WilliamKWusik/Wusik-44UM/Documents/DIY/Arduino Pro Micro.jpg

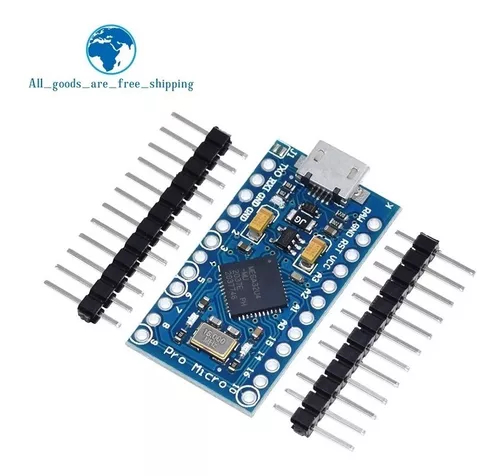
Documents/DIY/Arduino Pro Micro.jpg
