WilliamKWusik/Wusik-44UM/Documents/DIY/Button Switches.jpg

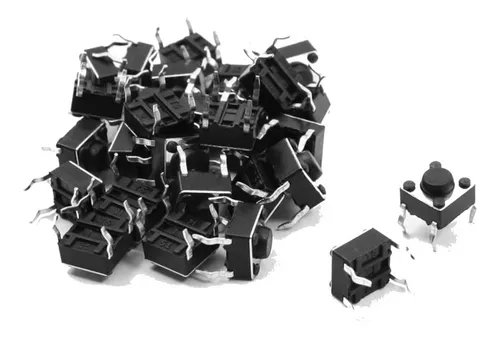
Documents/DIY/Button Switches.jpg
