WilliamKWusik/Wusik-44UM/Documents/DIY/LED Strip.jpg

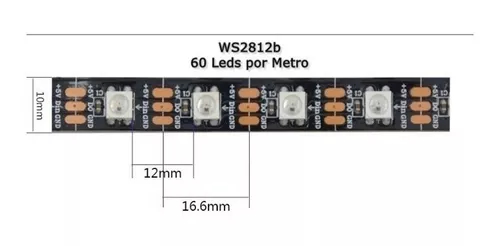
Documents/DIY/LED Strip.jpg
