WilliamKWusik/Wusik-44UM/Documents/DIY/Wires.jpg

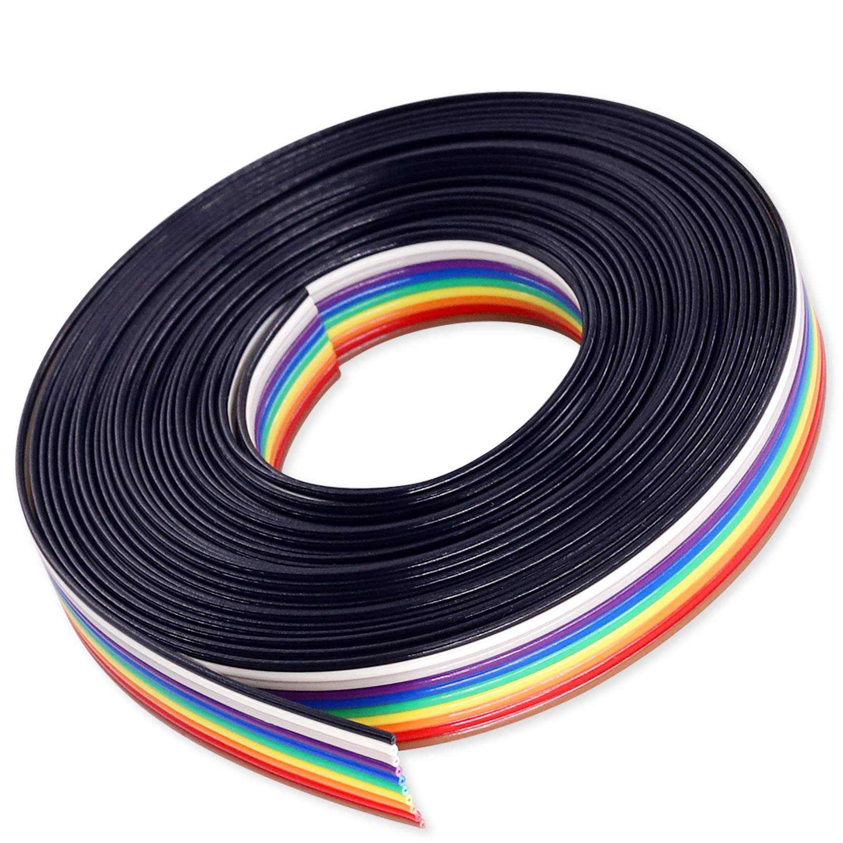
Documents/DIY/Wires.jpg
