WilliamKWusik/Wusik-44UM/Images/Picture (2).jpeg

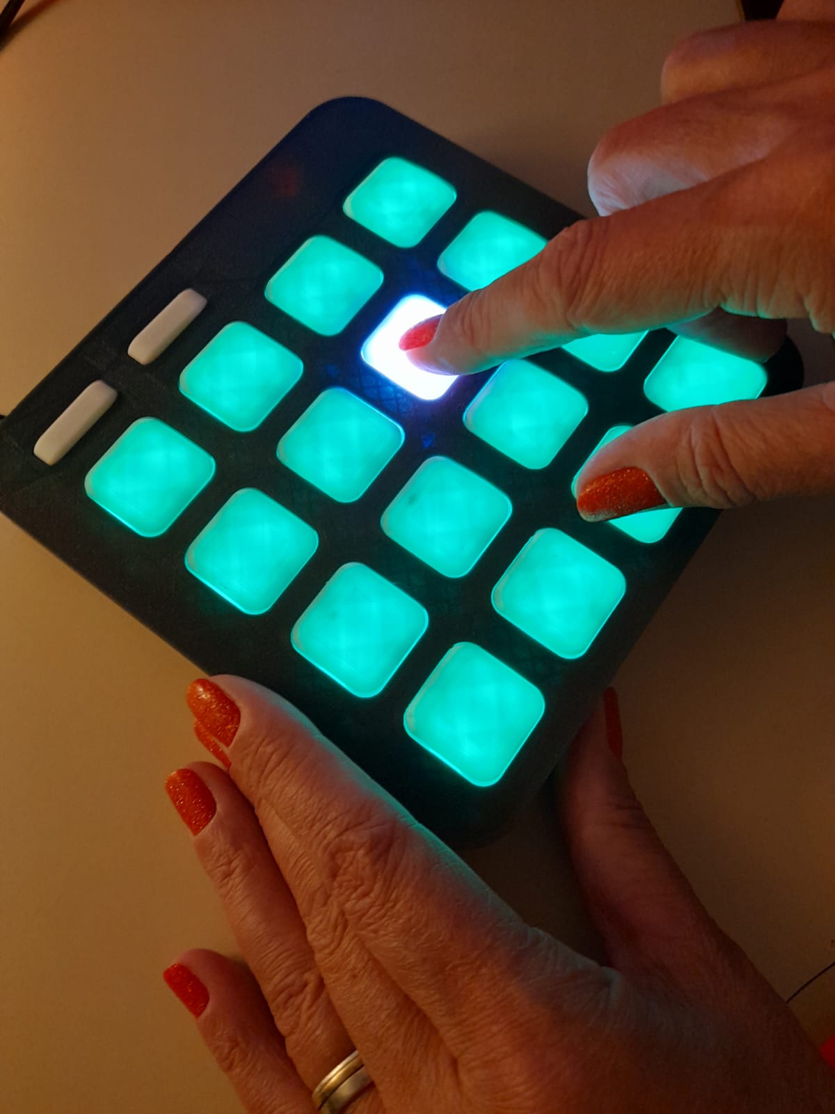
Images/Picture (2).jpeg
