WilliamKWusik/Wusik-44UM/Images/Picture (3).jpeg

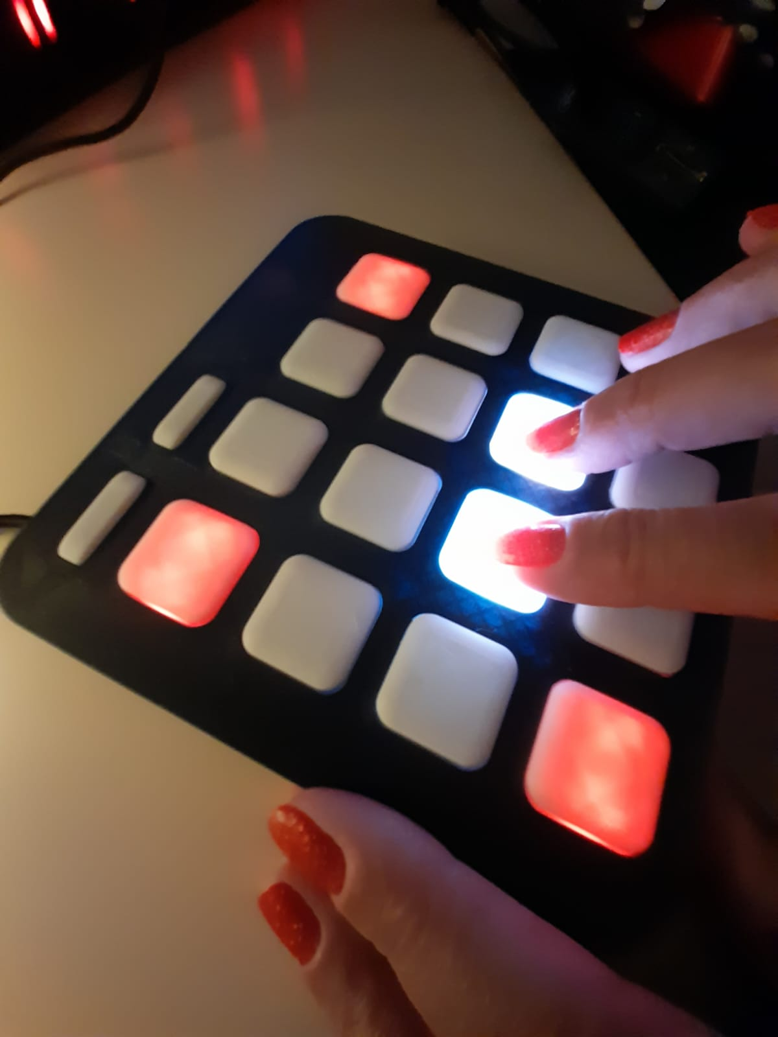
Images/Picture (3).jpeg
