WilliamKWusik/Wusik-44UM/Wusik_PR44_Performance_App/_Release/Wusik PR44 Data/Samples/PerimeterSound.com/Bio-MechanicBeats1_FreeSamplePack/_BioMechanicBeats_480.jpg

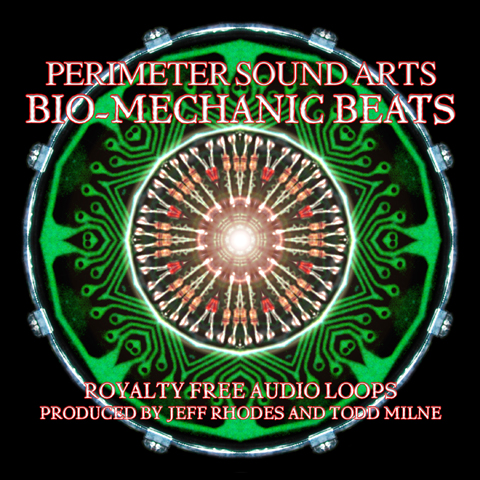
Wusik_PR44_Performance_App/_Release/Wusik PR44 Data/Samples/PerimeterSound.com/Bio-MechanicBeats1_FreeSamplePack/_BioMechanicBeats_480.jpg
