WilliamKWusik/Wusik-44UM/Wusik_PR44_Performance_App/_Release/Wusik PR44 Data/Samples/PerimeterSound.com/Bio-MechanicBeats2_FreeSamplePack/_Bio-MechanicBeats2_480.jpg

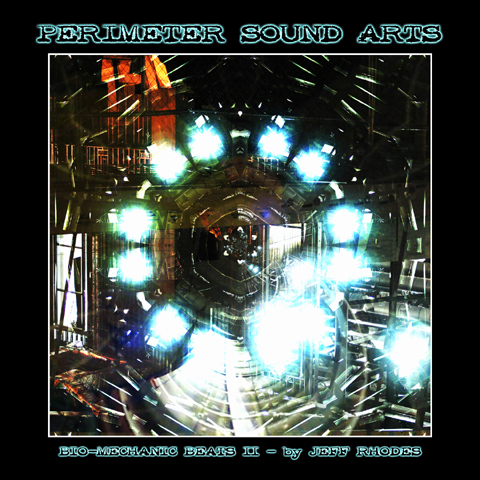
Wusik_PR44_Performance_App/_Release/Wusik PR44 Data/Samples/PerimeterSound.com/Bio-MechanicBeats2_FreeSamplePack/_Bio-MechanicBeats2_480.jpg
