WilliamKWusik/Wusik-44UM/Wusik_PR44_Performance_App/_Release/Wusik PR44 Data/Samples/PerimeterSound.com/Bio-MechanicBeats3_FreeSamplePack/Bio-MechanicBeatsIII_coverart_500X.jpg

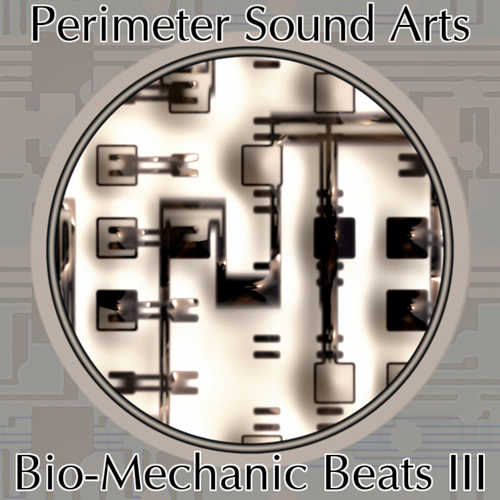
Wusik_PR44_Performance_App/_Release/Wusik PR44 Data/Samples/PerimeterSound.com/Bio-MechanicBeats3_FreeSamplePack/Bio-MechanicBeatsIII_coverart_500X.jpg
