WilliamKWusik/Wusik-44UM/Wusik_PR44_Performance_App/_Release/Wusik PR44 Data/Samples/PerimeterSound.com/AbstractWorld Fusion1_FreeSamplePack/_AbstractWorldFusion_480.jpg

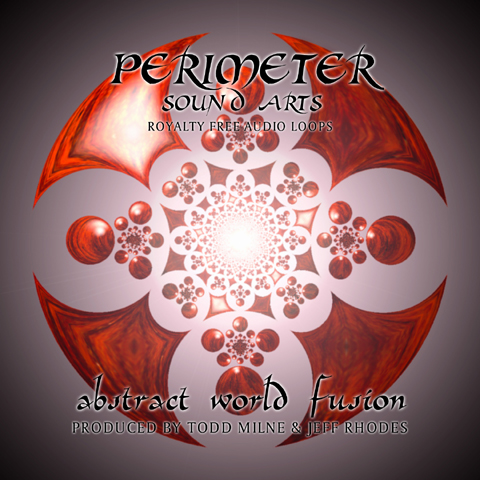
Wusik_PR44_Performance_App/_Release/Wusik PR44 Data/Samples/PerimeterSound.com/AbstractWorld Fusion1_FreeSamplePack/_AbstractWorldFusion_480.jpg
