WilliamKWusik/Wusik-44UM/Wusik_PR44_Performance_App/_Release/Wusik PR44 Data/Samples/PerimeterSound.com/AbstractWorldFusionIII_FreebeePack/Abstract World Fusion 3_large.jpg

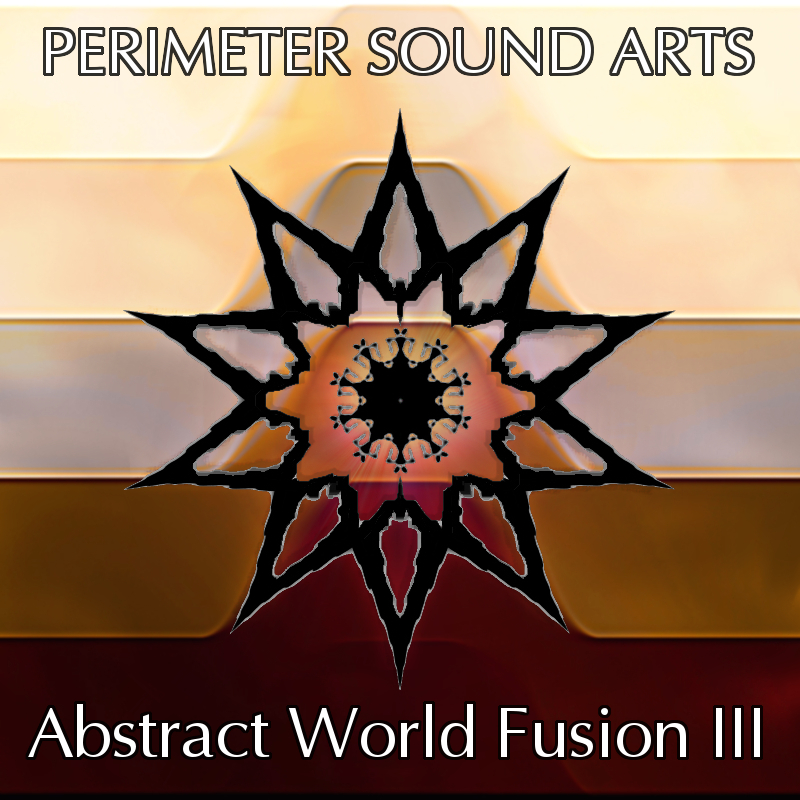
Wusik_PR44_Performance_App/_Release/Wusik PR44 Data/Samples/PerimeterSound.com/AbstractWorldFusionIII_FreebeePack/Abstract World Fusion 3_large.jpg
