WilliamKWusik/Wusik-44UM/Wusik_PR44_Performance_App/_Release/Wusik PR44 Data/Samples/PerimeterSound.com/Disturbance_FreeSamplePack/_Disturbance_480.jpg

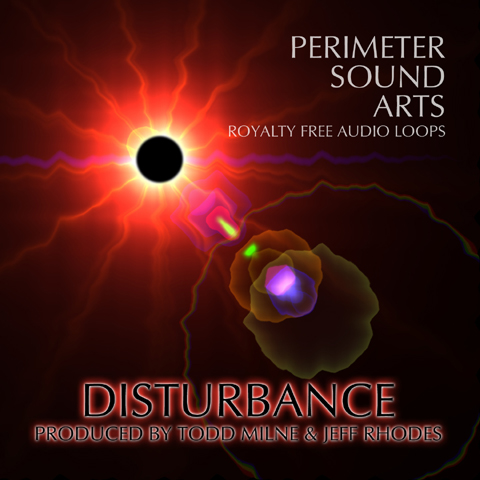
Wusik_PR44_Performance_App/_Release/Wusik PR44 Data/Samples/PerimeterSound.com/Disturbance_FreeSamplePack/_Disturbance_480.jpg
