WilliamKWusik/Wusik-44UM/Wusik_PR44_Performance_App/_Release/Wusik PR44 Data/Samples/Soundspice-FreeDemoLoops/Breakbeats-Structured1-FreebeeLoops/Breakbeats-Structured-Chapter1-450X.jpg

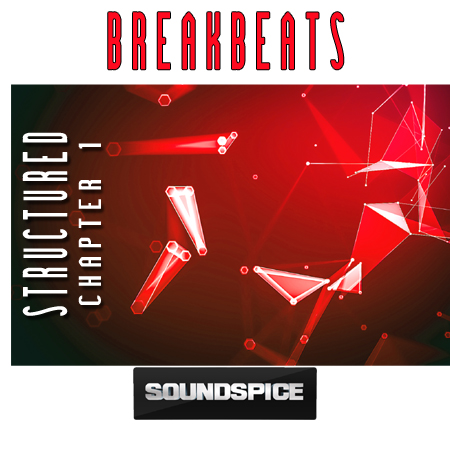
Wusik_PR44_Performance_App/_Release/Wusik PR44 Data/Samples/Soundspice-FreeDemoLoops/Breakbeats-Structured1-FreebeeLoops/Breakbeats-Structured-Chapter1-450X.jpg
