WilliamKWusik/Wusik-44UM/Wusik_PR44_Performance_App/_Release/Wusik PR44 Data/Samples/Soundspice-FreeDemoLoops/Breakbeats-Structured3-FreebeeLoops/Breakbeats-Structured-Chapter3-450X.jpg

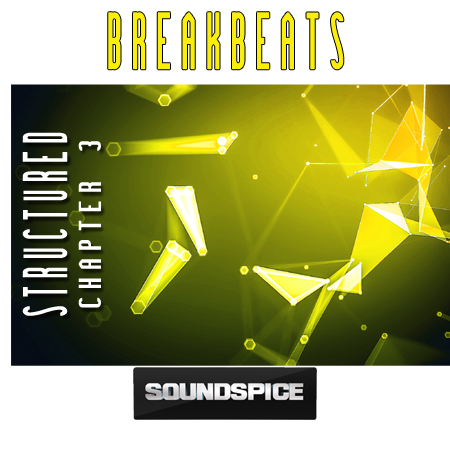
Wusik_PR44_Performance_App/_Release/Wusik PR44 Data/Samples/Soundspice-FreeDemoLoops/Breakbeats-Structured3-FreebeeLoops/Breakbeats-Structured-Chapter3-450X.jpg
