WilliamKWusik/Wusik-44UM/Wusik_PR44_Performance_App/_Release/Wusik PR44 Data/Samples/Soundspice-FreeDemoLoops/CartoonSwaggerVol1-FreePack/Cartoon Swagger vol1.jpg

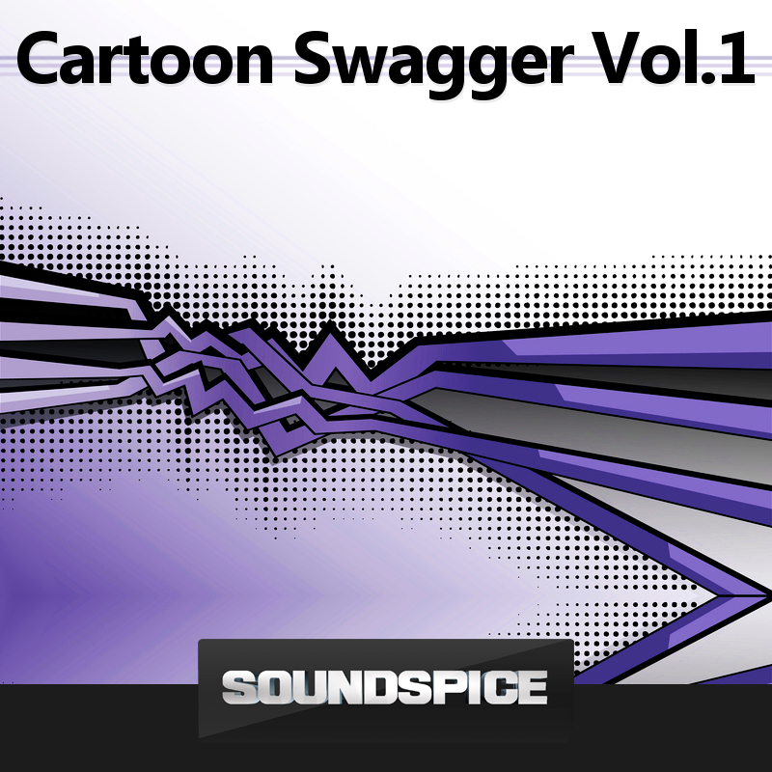
Wusik_PR44_Performance_App/_Release/Wusik PR44 Data/Samples/Soundspice-FreeDemoLoops/CartoonSwaggerVol1-FreePack/Cartoon Swagger vol1.jpg
