WilliamKWusik/Wusik-44UM/Wusik_PR44_Performance_App/_Release/Wusik PR44 Data/Samples/Soundspice-FreeDemoLoops/DarkSpeedDrum-n-BassVol1-FreePack/DarkSpeedVol1_800X.jpg

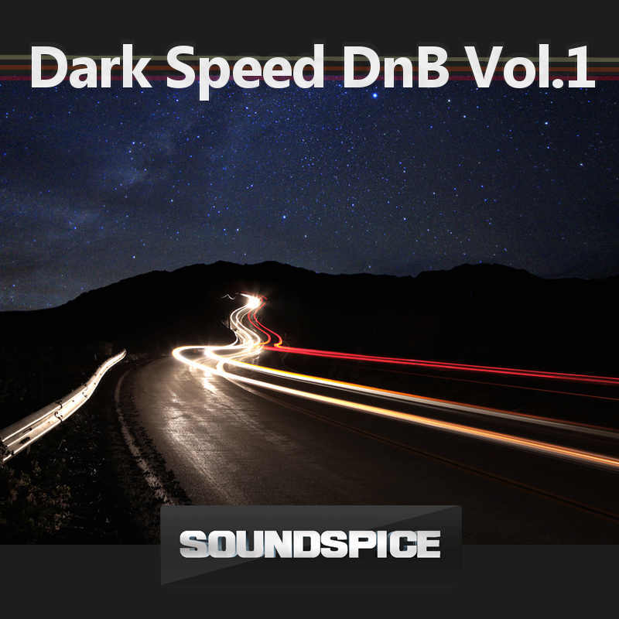
Wusik_PR44_Performance_App/_Release/Wusik PR44 Data/Samples/Soundspice-FreeDemoLoops/DarkSpeedDrum-n-BassVol1-FreePack/DarkSpeedVol1_800X.jpg
