WilliamKWusik/Wusik-44UM/Wusik_PR44_Performance_App/_Release/Wusik PR44 Data/Samples/Soundspice-FreeDemoLoops/DefectiveDance-Recharged(V1)-FreebeePack/DefectiveDance-Recharged-V1-1000X.jpg

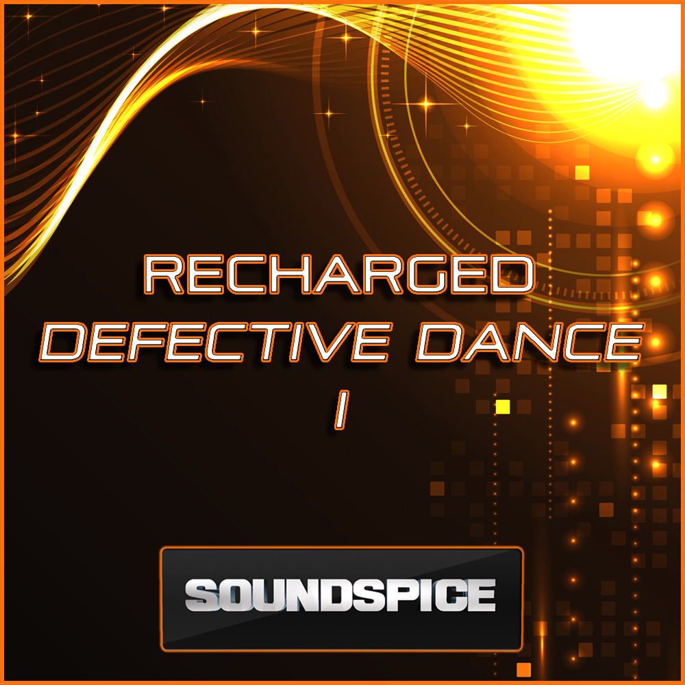
Wusik_PR44_Performance_App/_Release/Wusik PR44 Data/Samples/Soundspice-FreeDemoLoops/DefectiveDance-Recharged(V1)-FreebeePack/DefectiveDance-Recharged-V1-1000X.jpg
