WilliamKWusik/Wusik-44UM/Wusik_PR44_Performance_App/_Release/Wusik PR44 Data/Samples/Soundspice-FreeDemoLoops/DubExtractionVol1_FreebeePack/DubExtractionVol1_coverart_1000X.jpg

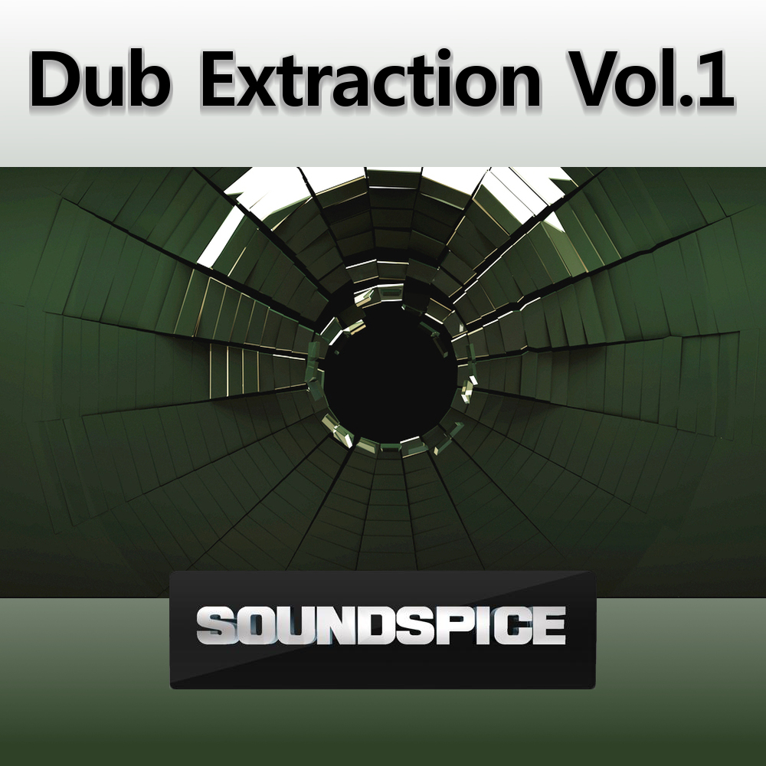
Wusik_PR44_Performance_App/_Release/Wusik PR44 Data/Samples/Soundspice-FreeDemoLoops/DubExtractionVol1_FreebeePack/DubExtractionVol1_coverart_1000X.jpg
