WilliamKWusik/Wusik-44UM/Wusik_PR44_Performance_App/_Release/Wusik PR44 Data/Samples/Soundspice-FreeDemoLoops/DubExtractionVol2_FreebeePack/Dub Extraction Vol 2 - 1000X.jpg

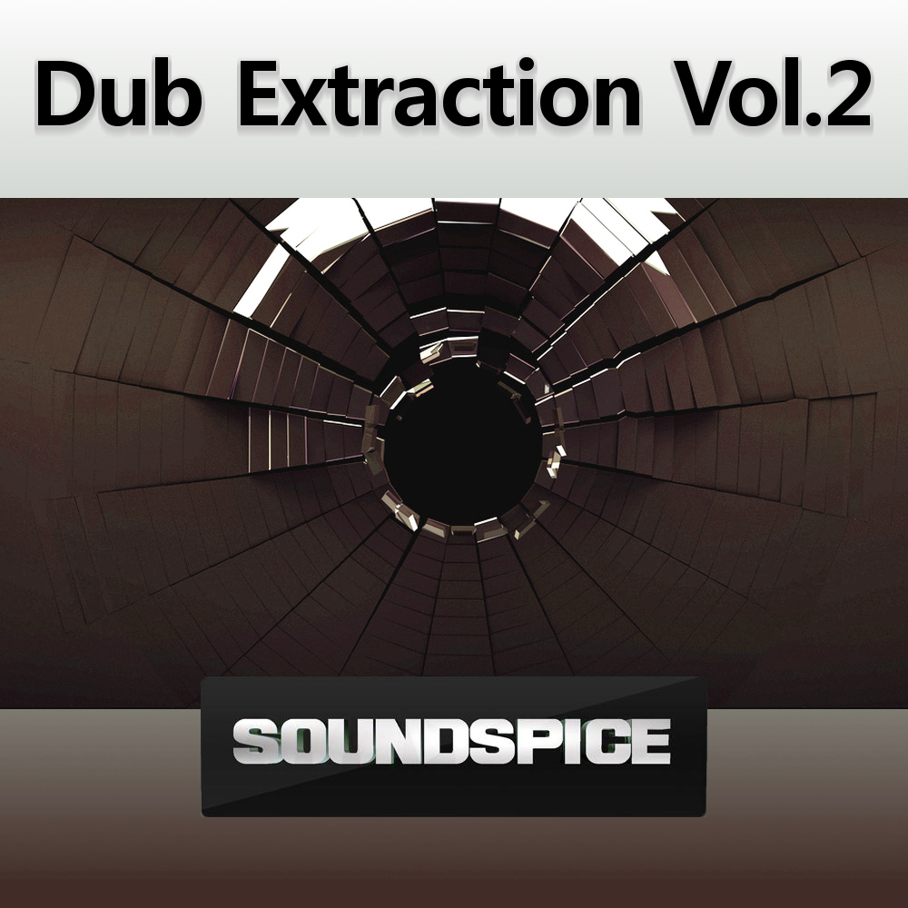
Wusik_PR44_Performance_App/_Release/Wusik PR44 Data/Samples/Soundspice-FreeDemoLoops/DubExtractionVol2_FreebeePack/Dub Extraction Vol 2 - 1000X.jpg
