WilliamKWusik/Wusik-44UM/Wusik_PR44_Performance_App/_Release/Wusik PR44 Data/Samples/Soundspice-FreeDemoLoops/IndustrialGlitchVol3-FreebeeLoops/IndustrialGlitchVol3-coverart-1000X.jpg

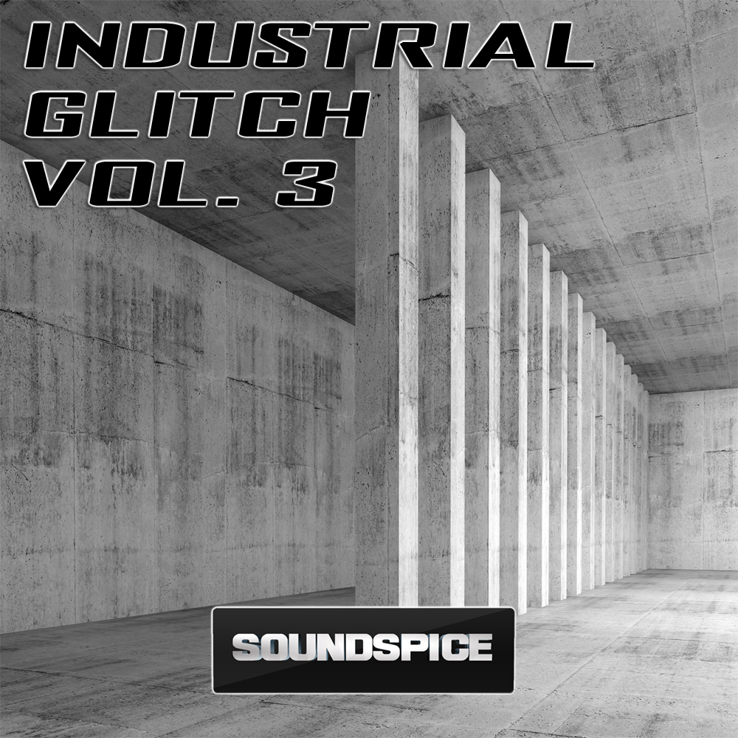
Wusik_PR44_Performance_App/_Release/Wusik PR44 Data/Samples/Soundspice-FreeDemoLoops/IndustrialGlitchVol3-FreebeeLoops/IndustrialGlitchVol3-coverart-1000X.jpg
