WilliamKWusik/Wusik-44UM/Wusik_PR44_Performance_App/_Release/Wusik PR44 Data/Samples/Soundspice-FreeDemoLoops/NeonCityDub-Vol1-FreebeeLoops/NeonCityDub-Vol1-1000X.jpg

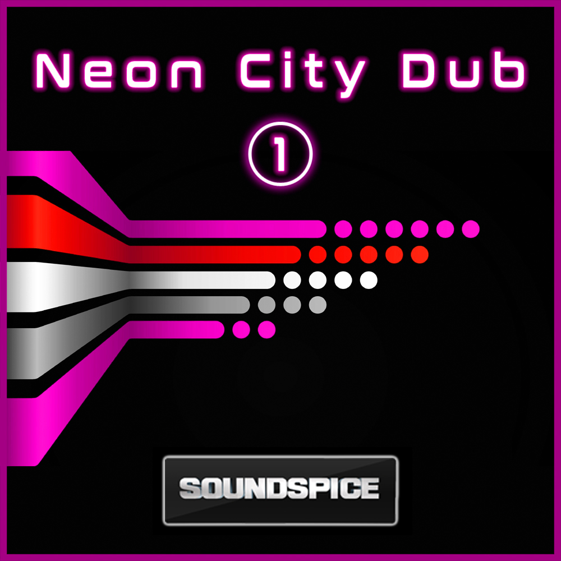
Wusik_PR44_Performance_App/_Release/Wusik PR44 Data/Samples/Soundspice-FreeDemoLoops/NeonCityDub-Vol1-FreebeeLoops/NeonCityDub-Vol1-1000X.jpg
