WilliamKWusik/Wusik-44UM/Wusik_PR44_Performance_App/_Release/Wusik PR44 Data/Samples/Soundspice-FreeDemoLoops/OtherSpaceIndustrialVol1_FreebeePack/Other Space Industrial Vol 1 - 1000x.jpg

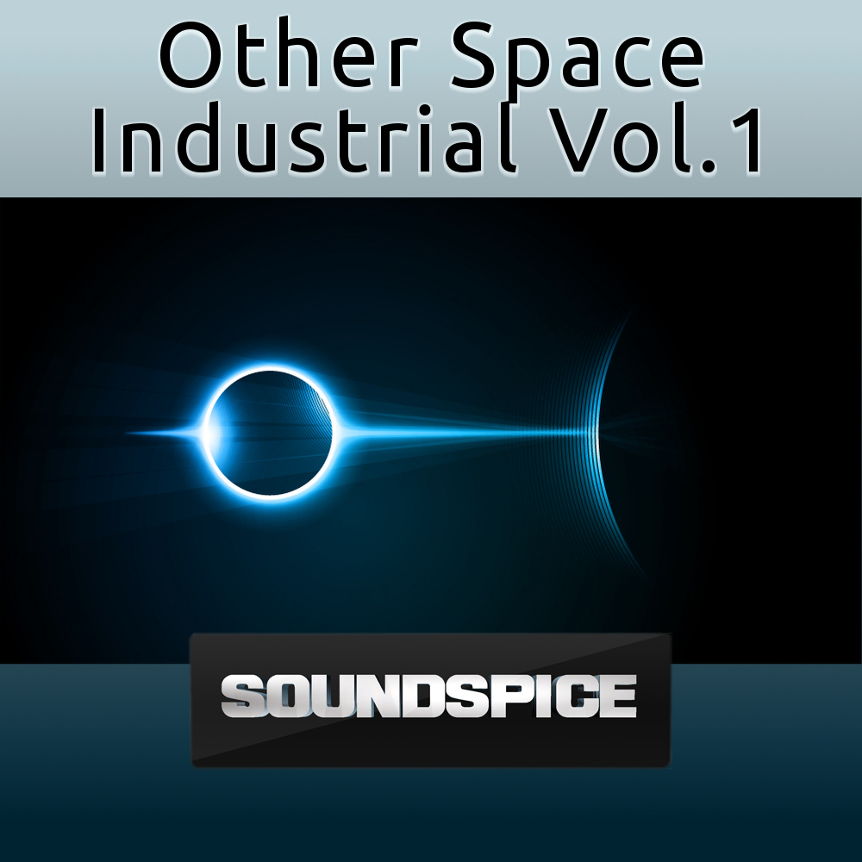
Wusik_PR44_Performance_App/_Release/Wusik PR44 Data/Samples/Soundspice-FreeDemoLoops/OtherSpaceIndustrialVol1_FreebeePack/Other Space Industrial Vol 1 - 1000x.jpg
