WilliamKWusik/Wusik-44UM/Wusik_PR44_Performance_App/_Release/Wusik PR44 Data/Samples/Soundspice-FreeDemoLoops/SuperNaturalGlitchHopVol1-FreePack/SuperNaturalGlitchHopVol1_800X.jpg

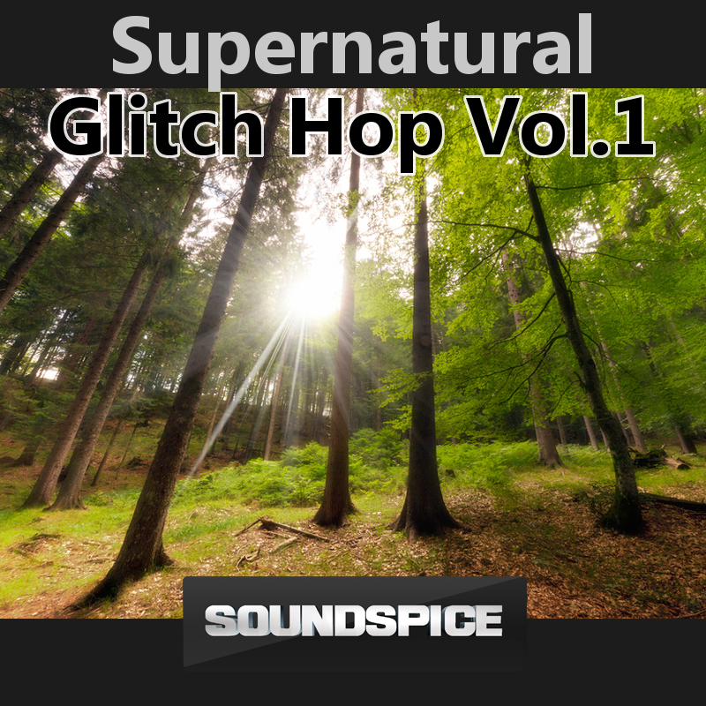
Wusik_PR44_Performance_App/_Release/Wusik PR44 Data/Samples/Soundspice-FreeDemoLoops/SuperNaturalGlitchHopVol1-FreePack/SuperNaturalGlitchHopVol1_800X.jpg
