WilliamKWusik/Wusik-44UM/Wusik_PR44_Performance_App/_Release/Wusik PR44 Data/Samples/Soundspice-FreeDemoLoops/SynthwaveRetro-Hindsight-Vol1-FreebeePack/Synthwave-HindsightVol1-1000X.jpg

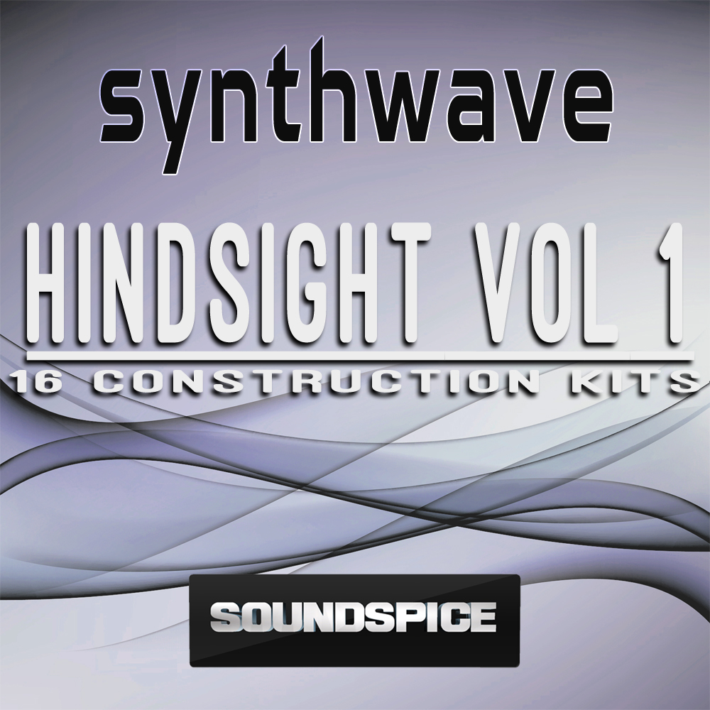
Wusik_PR44_Performance_App/_Release/Wusik PR44 Data/Samples/Soundspice-FreeDemoLoops/SynthwaveRetro-Hindsight-Vol1-FreebeePack/Synthwave-HindsightVol1-1000X.jpg
