WilliamKWusik/Wusik-44UM/Wusik_PR44_Performance_App/_Release/Wusik PR44 Data/Samples/Soundspice-FreeDemoLoops/TimeLapseTripHopVol2-FreebeePack/TimeLapse-TripHop-Vol2-1650X.jpg

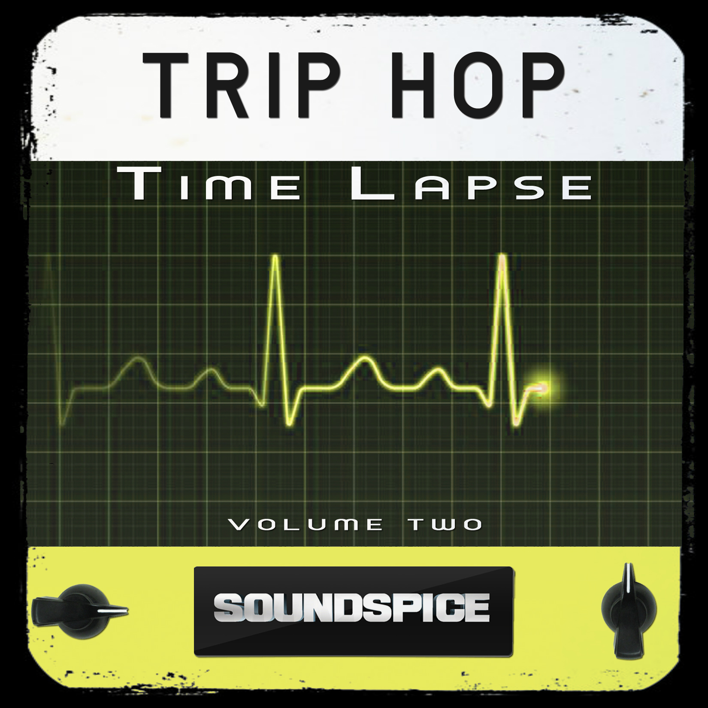
Wusik_PR44_Performance_App/_Release/Wusik PR44 Data/Samples/Soundspice-FreeDemoLoops/TimeLapseTripHopVol2-FreebeePack/TimeLapse-TripHop-Vol2-1650X.jpg
