WilliamKWusik/Wusik-44UM/Wusik_PR44_Performance_App/_Release/Wusik PR44 Data/Samples/Soundspice-FreeDemoLoops/TurbulentFlow-DNB-FreebeeLoops/TurbulentFlow-DrumNbass-600X.jpg

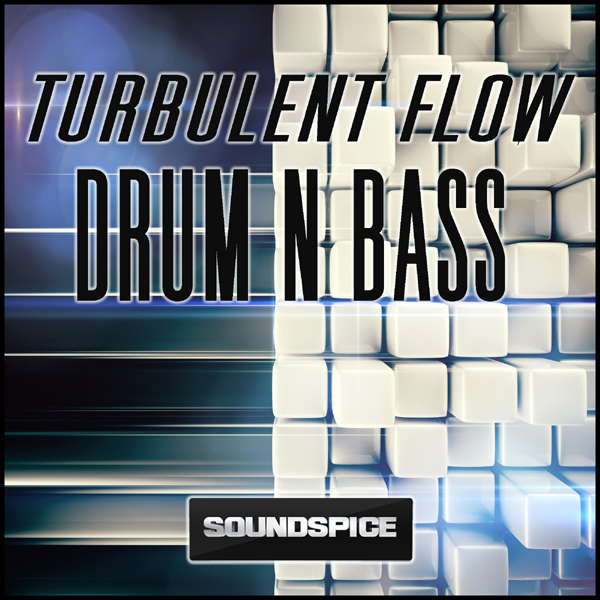
Wusik_PR44_Performance_App/_Release/Wusik PR44 Data/Samples/Soundspice-FreeDemoLoops/TurbulentFlow-DNB-FreebeeLoops/TurbulentFlow-DrumNbass-600X.jpg
