WilliamKWusik/Wusik-44UM/Wusik_PR44_Performance_App/_Release/Wusik PR44 Data/Samples/Soundspice-FreeDemoLoops/WorldTempoVol1-FreebeePack/WorldTempo-Vol1-cover_1000X.jpg

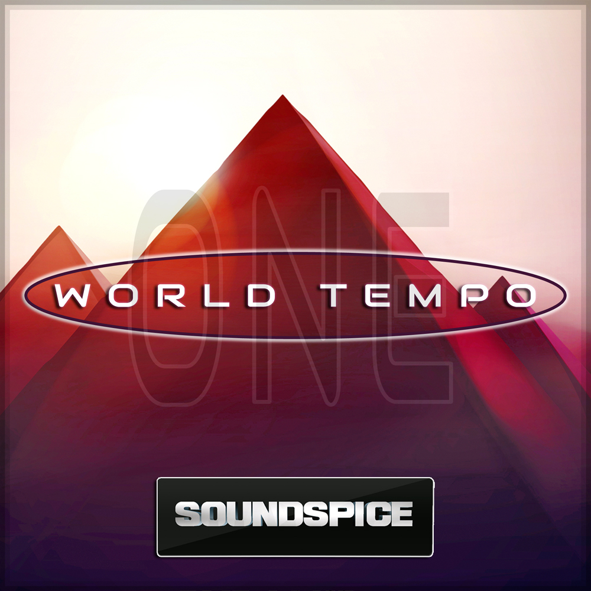
Wusik_PR44_Performance_App/_Release/Wusik PR44 Data/Samples/Soundspice-FreeDemoLoops/WorldTempoVol1-FreebeePack/WorldTempo-Vol1-cover_1000X.jpg
