WilliamKWusik/Wusik-44UM/Wusik_PR44_Performance_App/_Release/Wusik PR44 Data/Samples/Soundspice-FreeDemoLoops/WorldTempoVol3-FreebeePack/WorldTempo-Vol3-cover_1000X.jpg

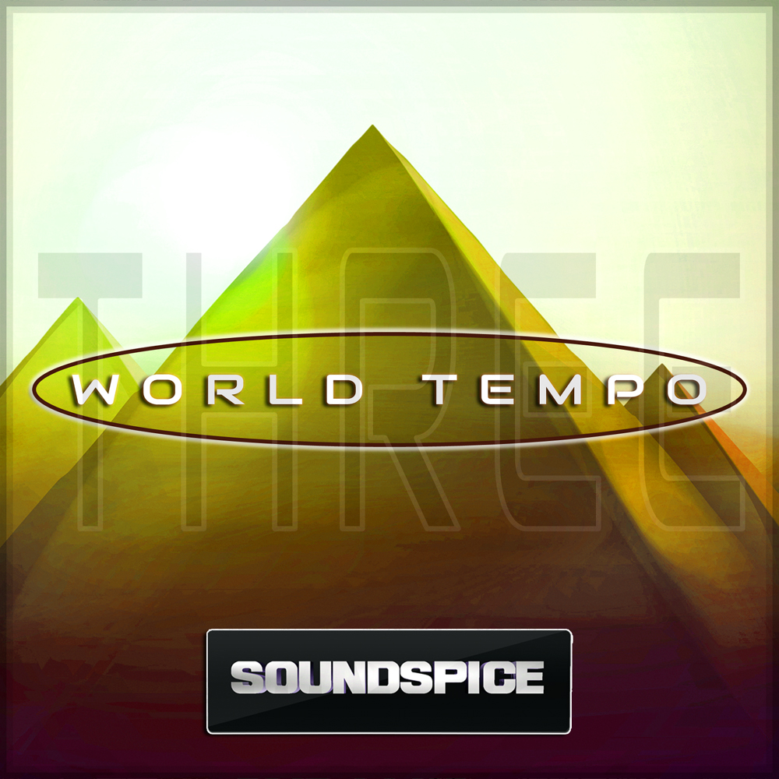
Wusik_PR44_Performance_App/_Release/Wusik PR44 Data/Samples/Soundspice-FreeDemoLoops/WorldTempoVol3-FreebeePack/WorldTempo-Vol3-cover_1000X.jpg
