WilliamKWusik/Wusik-44UM/Wusik_44UM_Arduino/RGB_LEDs.ino

/*
 * Created by William Kalfelz @ Wusik.com (c) 2023
 */
 //
// ------------------------------------------------------------------------------------------------------------------------------------
void RGBBlink()
{
  if (rgbBlink > 0)
  {
    rgbBlinkCounter++;
    rgbBlinkCounterFast++;
    //
    if (rgbBlinkCounterFast > RGB_BLINK_FAST)
    {
      bool hasOne = false;
      rgbBlinkCounterFast = 0;
      //
      for (byte xx = 0; xx < 16; xx++)
      {
        if (getVarBit(rgbBlinkFast, xx) && getVarBit(rgbBlink, xx))
        {  
          hasOne = true;       
          if (rgbBlinkStatusFast) colorPixelNoShow(xx, getColor(rgbBlinkColor[xx])); else colorPixelClearNoShow(xx);
        }
      }
      //
      rgbBlinkStatusFast = !rgbBlinkStatusFast;
      if (hasOne) strip.show();
    }
    //   
    if (rgbBlinkCounter > RGB_BLINK_SLOW)
    {
      bool hasOne = false;
      rgbBlinkCounter = 0;
      //
      for (byte xx = 0; xx < 16; xx++)
      {
        if (!getVarBit(rgbBlinkFast, xx) && getVarBit(rgbBlink, xx))
        {         
          hasOne = true;
          if (rgbBlinkStatus) colorPixelNoShow(xx, getColor(rgbBlinkColor[xx])); else colorPixelClearNoShow(xx);
        }
      }
      //
      rgbBlinkStatus = !rgbBlinkStatus;
      if (hasOne) strip.show();
    }
  }
}
//
// ------------------------------------------------------------------------------------------------------------------------------------
void updateButtonsOffColor()
{
  if (turnOffButtonLEDs) return;
  //
  strip.clear();
  //
  for (byte xx = 0; xx < 16; xx++)
  {
    if (buttonsStruct[currentPage][xx + 2].type == kNoteOnOffLatch)
    {
      if (buttonsStruct[currentPage][xx + 2].valueChar == 1)
      {
        strip.setPixelColor(rgbLEDsList[xx][0], getColor(buttonsStruct[currentPage][xx + 2].colorOn));
        strip.setPixelColor(rgbLEDsList[xx][1], getColor(buttonsStruct[currentPage][xx + 2].colorOn));       
      }
      else
      {
        strip.setPixelColor(rgbLEDsList[xx][0], getColor(buttonsStruct[currentPage][xx + 2].colorOff));
        strip.setPixelColor(rgbLEDsList[xx][1], getColor(buttonsStruct[currentPage][xx + 2].colorOff));        
      }
    }
    else
    {
      strip.setPixelColor(rgbLEDsList[xx][0], getColor(buttonsStruct[currentPage][xx + 2].colorOff));
      strip.setPixelColor(rgbLEDsList[xx][1], getColor(buttonsStruct[currentPage][xx + 2].colorOff));
    }
  }
  //
  strip.show();
}
//
// ------------------------------------------------------------------------------------------------------------------------------------
uint32_t getColor(byte colorID)
{
  uint32_t returnColor = 0;
  //
  switch(colorID)
  {
    case kOff:        returnColor = strip.Color(  0,   0,   0); break;
    case kWhite:      returnColor = strip.Color(255, 255, 255); break;
    case kRed:        returnColor = strip.Color(255,   0,   0); break;
    case kGreen:      returnColor = strip.Color(  0, 255,   0); break;
    case kBlue:       returnColor = strip.Color(  0,   0, 255); break;
    case kRed_Soft:   returnColor = strip.Color( 25,   0,   0); break;
    case kGreen_Soft: returnColor = strip.Color(  0,  25,   0); break;
    case kBlue_Soft:  returnColor = strip.Color(  0,   0,  25); break;
  }
  //
  return returnColor;
}
//
// ------------------------------------------------------------------------------------------------------------------------------------
void colorPixels(uint32_t color)
{
  for(int i=0; i<strip.numPixels(); i++) 
  {
    strip.setPixelColor(i, color);
  }
  //
  strip.show();
}
//
// ------------------------------------------------------------------------------------------------------------------------------------
void clearPixels()
{
  strip.clear();
  strip.show();
}
//
// ------------------------------------------------------------------------------------------------------------------------------------
void colorPixelWhite(byte pixel)
{
  strip.setPixelColor(rgbLEDsList[pixel][0], strip.Color(255,   255,   255));
  strip.setPixelColor(rgbLEDsList[pixel][1], strip.Color(255,   255,   255));
  strip.show();
}
//
// ------------------------------------------------------------------------------------------------------------------------------------
void colorPixelClear(byte pixel)
{
  strip.setPixelColor(rgbLEDsList[pixel][0], strip.Color(0,   0,   0));
  strip.setPixelColor(rgbLEDsList[pixel][1], strip.Color(0,   0,   0));
  strip.show();
}
//
// ------------------------------------------------------------------------------------------------------------------------------------
void colorPixelClearNoShow(byte pixel)
{
  strip.setPixelColor(rgbLEDsList[pixel][0], strip.Color(0,   0,   0));
  strip.setPixelColor(rgbLEDsList[pixel][1], strip.Color(0,   0,   0));
}
//
// ------------------------------------------------------------------------------------------------------------------------------------
void colorPixel(byte pixel, uint32_t color)
{
  strip.setPixelColor(rgbLEDsList[pixel][0], color);
  strip.setPixelColor(rgbLEDsList[pixel][1], color);
  strip.show();
}
//
// ------------------------------------------------------------------------------------------------------------------------------------
void colorPixelNoShow(byte pixel, uint32_t color)
{
  strip.setPixelColor(rgbLEDsList[pixel][0], color);
  strip.setPixelColor(rgbLEDsList[pixel][1], color);
}
//
// ------------------------------------------------------------------------------------------------------------------------------------
void flashRed(byte times)
{
  for (byte xx = 0; xx < times; xx++)
  {
    colorPixels(strip.Color(255,   0,   0)); // Red
    delay(50);
    colorPixels(strip.Color(255,   255,   255)); // White
    delay(50);
    colorPixels(strip.Color(0,   0,   0)); // Off
    delay(50);
  }
}
//
// ------------------------------------------------------------------------------------------------------------------------------------
#if INTRO_ANIMATION
  void pixelsIntroAnimation()
  {
    for (byte xx = 0; xx < 16; xx++)
    {
      colorPixelWhite(rgbsIntroAnimation[xx]);
      delay(INTRO_ANIMATION_SPEED);
    }
    //
    delay(INTRO_ANIMATION_SPEED_HOLD);
    //
    for (byte xx = 0; xx < 16; xx++)
    {
      strip.setPixelColor(rgbLEDsList[rgbsIntroAnimation[xx]][0], strip.Color(255, 0, 0));
      strip.setPixelColor(rgbLEDsList[rgbsIntroAnimation[xx]][1], strip.Color(255, 0, 0));
      //
      strip.show();
      delay(INTRO_ANIMATION_SPEED);
    }
    //
    int redS[16];
    for (byte xx = 0; xx < 16; xx++) { redS[xx] = 255; }
    //
    while (1)
    {
      for (byte xx = 0; xx < 16; xx++)
      {
        redS[xx] -= random(0, 50);
        if (redS[xx] < 0) redS[xx] = 0;
        //
        strip.setPixelColor(rgbLEDsList[xx][0], strip.Color(redS[xx], 0, 0));
        strip.setPixelColor(rgbLEDsList[xx][1], strip.Color(redS[xx], 0, 0));
      }
      //
      strip.show();
      delay(80);
      //
      bool allZero = true;
      for (byte xx = 0; xx < 16; xx++) { if (redS[xx] > 0) { allZero = false; break; } }
      if (allZero) break;
    }
    //
    clearPixels();
  }
#endif
